CREPP-PLOEMEUR/CREPP.io/PCB/CCR/CCR.png

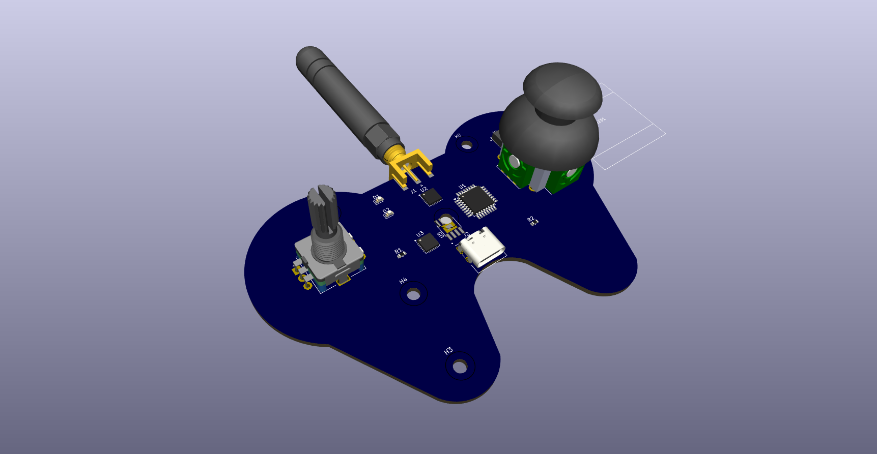
PCB/CCR/CCR.png
